daverowntree/WifeClock/Hardware/clock_VeeCAD.sch

## KiCad design Hardware/clock_VeeCAD.sch (2014-01-10)

Schematic: clock_VeeCAD.sch

Parts:
C1, C2: 22p; AX1_1
C3, C5, C6: 100n; AX1_1
C4: 10u; RA1_2
D1, D3, D4, D5, D6, D7, D8, D9, D10, D11, D12, D13, D14, D15, D16, D17, D18, D19, D20, D21, D22, D23, D24, D26: LED; RA1_2
D2: 1N400X; AX3_1
K1: CONN_3; SIP3
P1: RF Module; SIP4
P2: programmer; SIP6
P3: CONN_1; SIP1
P4: Tiny RTC; SIP5
Q1, Q3, Q4, Q5, Q6, Q7, Q8: 2N5401; TO92
Q2, Q9, Q10, Q11, Q12: 2N2222; TO92
R1, R4, R5, R8, R10, R12, R13, R16, R17, R19, R21, R25: 4k7; AX3_1N
R2, R6, R14, R18: 33R; AX3_1N
R3, R7, R9, R11, R15, R20, R24: 2k7; AX3_1N
R22: 47R; AX3_1N
R23: 100k; AX3_1N
R27: 100R; AX3_1N
SW1: Reset; TACT_01
U1: ATMEGA8; DIP28N
X1: 16 MHz; AX1_1

Notes on the sheet:
Digit Separator
To cathode connection of other 3 digits
1: Vcc 2: Data 3: ? 4: Gnd
P1a/1: RST 2: 3V3 3: 5V 4: TXD 5: RXD 6: Gnd P1b/1: DTR
Decoupling: Close to IC1
1: Gnd 2: Vcc 3: SDA 4: SCL 5: DS
LED: Vf=3v0 to 3v2 If=20mA
pwm
activity
Ext 5V In
seg1
seg2
seg3
seg4
seg5
seg6
seg7
digit1
digit2
digit3
digit4
digit0
