daverowntree/WifeClock/Software/display.h

void update_portb();
void update_portc();
void update_portd();
void init_display();
int time_to_digits(char *dig1, char *dig2, char *dig3, char *dig4);
void scan_display(void);
void blank_display(void);
void write_segs(char n);
